Draganito/kicad-mcp/crates/kicad-mcp/src/pads.rs

//! Pad truth and footprint moves, straight from the board.
//!
//! `board_pads` decodes the raw `FootprintInstance` protos KiCad returns
//! over IPC — the **baked** pad positions, not template math. This is the
//! verification tool: a mirrored or mis-rotated part shows up here as pads
//! on the wrong side of the anchor, no 3D render needed.
//!
//! `move_footprint` applies a rigid transform (translate + rotate about the
//! anchor) to the instance and every nested pad, then `UpdateItems` the
//! whole footprint — the same splice path as `connect_pins`, so nets,
//! padstack geometry and the reference survive. No remove+place.

use std::collections::HashMap;

use prost::Message;
use prost_types::Any;

use crate::kicad::Kicad;
use crate::proto_wire::{map_len_fields, set_len_field};

const NM_PER_MM: f64 = 1_000_000.0;
const TYPE_PAD: &str = "type.googleapis.com/kiapi.board.types.Pad";

// Layer / enum codes as in place.rs (kiapi.board.types).
const BL_F_CU: i32 = 3;
const BL_B_CU: i32 = 34;
const PT_PTH: i32 = 1;
const PT_SMD: i32 = 2;
const PT_NPTH: i32 = 4;
const PSS_CIRCLE: i32 = 1;
const PSS_RECTANGLE: i32 = 2;
const PSS_OVAL: i32 = 3;

fn nm_to_mm(nm: i64) -> f64 {
    nm as f64 / NM_PER_MM
}

fn mm_to_nm(mm: f64) -> i64 {
    (mm * NM_PER_MM).round() as i64
}

fn round4(v: f64) -> f64 {
    (v * 10_000.0).round() / 10_000.0
}

#[derive(Debug, Clone, serde::Serialize)]
pub struct PadRow {
    pub reference: String,
    pub pin: String,
    pub net: String,
    pub x_mm: f64,
    pub y_mm: f64,
    pub width_mm: f64,
    pub height_mm: f64,
    pub rotation_deg: f64,
    /// `smd`, `pth`, or `npth`.
    pub kind: String,
    /// `rect`, `oval`, `circle`.
    pub shape: String,
    pub layer: String,
    /// Every copper layer this pad exists on (`F.Cu`, `In1.Cu`, …).
    /// Through-hole wire pads should list the inners — a 5V PTH without
    /// `In1.Cu` cannot take thermals from the power pour.
    pub layers: Vec<String>,
    #[serde(skip_serializing_if = "Option::is_none")]
    pub drill_mm: Option<f64>,
    /// Slot length for oblong drills; absent for round holes.
    #[serde(skip_serializing_if = "Option::is_none")]
    pub drill_h_mm: Option<f64>,
}

/// Baked pad rows for every footprint on the board (IPC raw protos, the
/// positions KiCad actually draws). Optional reference / net filters.
pub async fn board_pads(
    k: &Kicad,
    reference: Option<&str>,
    net: Option<&str>,
) -> Result<Vec<PadRow>, String> {
    let fps = k.footprints().await?;
    let mut ref_of: HashMap<String, String> = HashMap::new();
    for fp in &fps {
        if let (Some(id), Some(r)) = (fp.id.as_deref(), fp.reference.as_deref()) {
            ref_of.insert(id.to_string(), r.to_string());
        }
    }
    let mut net_of: HashMap<String, String> = HashMap::new();
    for entry in k.pad_netlist().await.unwrap_or_default() {
        if let Some(id) = entry.pad_id {
            net_of.insert(id, entry.net_name.unwrap_or_default());
        }
    }
    let copper_count = k
        .summary()
        .await
        .ok()
        .and_then(|s| s.copper_layer_count)
        .unwrap_or(2);
    let raws = k
        .raw_items(vec![kicad_ipc_rs::PcbObjectTypeCode::new_footprint().code])
        .await?;
    let mut rows = Vec::new();
    for raw in &raws {
        let inst = FpInstDec::decode(raw.value.as_slice())
            .map_err(|e| format!("footprint proto decode: {e}"))?;
        let fp_ref = inst
            .id
            .as_ref()
            .and_then(|id| ref_of.get(&id.value))
            .cloned()
            .unwrap_or_default();
        if let Some(want) = reference {
            if fp_ref != want {
                continue;
            }
        }
        let Some(def) = inst.definition else {
            continue;
        };
        for item in &def.items {
            let Some(pad) = decode_pad(item) else {
                continue;
            };
            let pad_net = pad
                .id
                .as_ref()
                .and_then(|id| net_of.get(&id.value))
                .cloned()
                .unwrap_or_default();
            if let Some(want) = net {
                if pad_net != want {
                    continue;
                }
            }
            let pos = pad.position.unwrap_or_default();
            let stack = pad.pad_stack.unwrap_or_default();
            let copper = stack.copper_layers.first();
            let size = copper.and_then(|c| c.size.clone()).unwrap_or_default();
            let copper_ids: Vec<i32> = stack.copper_layers.iter().map(|c| c.layer).collect();
            let layer_ids = crate::copper::copper_layer_ids_from_stack(
                &stack.layers,
                &copper_ids,
                copper_count,
            );
            let layers: Vec<String> = layer_ids
                .iter()
                .copied()
                .map(crate::copper::layer_name)
                .collect();
            rows.push(PadRow {
                reference: fp_ref.clone(),
                pin: pad.number.clone(),
                net: pad_net,
                x_mm: round4(nm_to_mm(pos.x_nm)),
                y_mm: round4(nm_to_mm(pos.y_nm)),
                width_mm: round4(nm_to_mm(size.x_nm)),
                height_mm: round4(nm_to_mm(size.y_nm)),
                rotation_deg: stack.angle.map(|a| a.value_degrees).unwrap_or(0.0),
                kind: match pad.r#type {
                    PT_PTH => "pth",
                    PT_NPTH => "npth",
                    PT_SMD => "smd",
                    _ => "?",
                }
                .into(),
                shape: match copper.map(|c| c.shape) {
                    Some(PSS_CIRCLE) => "circle",
                    Some(PSS_OVAL) => "oval",
                    Some(PSS_RECTANGLE) => "rect",
                    _ => "?",
                }
                .into(),
                layer: layers
                    .first()
                    .cloned()
                    .unwrap_or_else(|| match copper.map(|c| c.layer) {
                        Some(BL_B_CU) => "B.Cu".into(),
                        Some(BL_F_CU) => "F.Cu".into(),
                        Some(other) => format!("L{other}"),
                        None => "?".into(),
                    }),
                layers,
                drill_mm: stack
                    .drill
                    .as_ref()
                    .and_then(|d| d.diameter.as_ref())
                    .map(|v| round4(nm_to_mm(v.x_nm)))
                    .filter(|d| *d > 0.0),
                drill_h_mm: stack
                    .drill
                    .as_ref()
                    .and_then(|d| d.diameter.as_ref())
                    .filter(|v| v.x_nm > 0 && v.y_nm != v.x_nm)
                    .map(|v| round4(nm_to_mm(v.y_nm))),
            });
        }
    }
    rows.sort_by(|a, b| {
        (natural_ref(&a.reference), a.pin.parse::<u32>().ok(), &a.pin).cmp(&(
            natural_ref(&b.reference),
            b.pin.parse::<u32>().ok(),
            &b.pin,
        ))
    });
    Ok(rows)
}

/// `U14` → (`U`, 14) so U2 sorts before U14.
fn natural_ref(r: &str) -> (String, u32) {
    let prefix: String = r.chars().take_while(|c| c.is_ascii_alphabetic()).collect();
    let num = r[prefix.len()..].parse::<u32>().unwrap_or(0);
    (prefix, num)
}

/// Rigid transform in KiCad's y-down frame with visually-CCW positive
/// angles — the same rotation sense as `place::world_xy`. A point at
/// `(px, py)` rides along when the anchor moves from `old` to `new` and
/// the part turns by `delta_deg`.
pub(crate) fn rigid_xy(
    px: f64,
    py: f64,
    old_anchor: (f64, f64),
    new_anchor: (f64, f64),
    delta_deg: f64,
) -> (f64, f64) {
    let rad = delta_deg.to_radians();
    let (s, c) = (rad.sin(), rad.cos());
    let dx = px - old_anchor.0;
    let dy = py - old_anchor.1;
    (
        new_anchor.0 + c * dx + s * dy,
        new_anchor.1 - s * dx + c * dy,
    )
}

/// Patch a raw `FootprintInstance` Any: anchor, orientation, every nested
/// pad (position + padstack angle) and the reference/value text positions.
/// Pure splice — everything not touched (nets, padstack geometry, KIIDs)
/// passes through byte-identical. Returns the patched Any and how many
/// pads were transformed.
pub fn transform_footprint_any(
    fp: &Any,
    old: (f64, f64, f64),
    new: (f64, f64, f64),
) -> Result<(Any, usize), String> {
    let old_anchor = (old.0, old.1);
    let new_anchor = (new.0, new.1);
    let delta_deg = new.2 - old.2;
    let pads_moved = std::cell::Cell::new(0usize);

    // Instance anchor + orientation.
    let mut value = set_len_field(&fp.value, 2, &encode_vec2(new.0, new.1))?;
    value = set_len_field(&value, 3, &encode_angle(new.2))?;

    // Reference/value text on the instance (fields 7/8).
    for field in [7u32, 8u32] {
        value = map_len_fields(&value, field, |f| {
            patch_field_text_pos(f, old_anchor, new_anchor, delta_deg)
        })?;
    }

    // Definition: nested pads + its own reference/value fields.
    value = map_len_fields(&value, 6, |def| {
        let mut def = map_len_fields(def, 11, |item_bytes| {
            let item = match Any::decode(item_bytes) {
                Ok(item) => item,
                Err(_) => return Ok(item_bytes.to_vec()),
            };
            let Some(pad) = decode_pad(&item) else {
                return Ok(item_bytes.to_vec());
            };
            let pos = pad.position.unwrap_or_default();
            let (nx, ny) = rigid_xy(
                nm_to_mm(pos.x_nm),
                nm_to_mm(pos.y_nm),
                old_anchor,
                new_anchor,
                delta_deg,
            );
            let mut pad_value = set_len_field(&item.value, 7, &encode_vec2(nx, ny))?;
            if delta_deg.abs() > 1e-9 {
                let new_angle = pad
                    .pad_stack
                    .as_ref()
                    .and_then(|s| s.angle.as_ref())
                    .map(|a| a.value_degrees)
                    .unwrap_or(0.0)
                    + delta_deg;
                pad_value = map_len_fields(&pad_value, 6, |stack| {
                    set_len_field(stack, 6, &encode_angle(new_angle))
                })?;
            }
            pads_moved.set(pads_moved.get() + 1);
            let patched = Any {
                type_url: if item.type_url.is_empty() {
                    TYPE_PAD.into()
                } else {
                    item.type_url
                },
                value: pad_value,
            };
            Ok(patched.encode_to_vec())
        })?;
        for field in [7u32, 8u32] {
            def = map_len_fields(&def, field, |f| {
                patch_field_text_pos(f, old_anchor, new_anchor, delta_deg)
            })?;
        }
        Ok(def)
    })?;

    if pads_moved.get() == 0 {
        return Err(
            "footprint proto has no pads — refusing a move that would strand copper".into(),
        );
    }
    Ok((
        Any {
            type_url: fp.type_url.clone(),
            value,
        },
        pads_moved.get(),
    ))
}

/// Field (tag 3 BoardText → tag 2 Text → tag 2 position): ride the text
/// along with the part so the silk refdes does not stay behind.
fn patch_field_text_pos(
    field_bytes: &[u8],
    old_anchor: (f64, f64),
    new_anchor: (f64, f64),
    delta_deg: f64,
) -> Result<Vec<u8>, String> {
    map_len_fields(field_bytes, 3, |board_text| {
        map_len_fields(board_text, 2, |text| {
            let decoded = TextDec::decode(text).unwrap_or_default();
            let Some(pos) = decoded.position else {
                return Ok(text.to_vec());
            };
            let (nx, ny) = rigid_xy(
                nm_to_mm(pos.x_nm),
                nm_to_mm(pos.y_nm),
                old_anchor,
                new_anchor,
                delta_deg,
            );
            set_len_field(text, 2, &encode_vec2(nx, ny))
        })
    })
}

/// Move / rotate one placed footprint. Courtyard-checked at the target,
/// nets untouched, one undo. Copper does not move.
pub async fn move_footprint(
    k: &Kicad,
    reference: &str,
    x_mm: f64,
    y_mm: f64,
    rotation_deg: Option<f64>,
) -> Result<serde_json::Value, String> {
    let fps = k.footprints().await?;
    let me = fps
        .iter()
        .find(|f| f.reference.as_deref() == Some(reference))
        .ok_or_else(|| format!("{reference} is not on the board"))?;
    let id = me
        .id
        .clone()
        .ok_or_else(|| format!("{reference} has no KIID over IPC"))?;
    let old = (
        me.x_mm.unwrap_or(0.0),
        me.y_mm.unwrap_or(0.0),
        me.rotation_deg.unwrap_or(0.0),
    );
    let new_rot = rotation_deg.unwrap_or(old.2);

    // Courtyard check at the target, against everything except this part.
    let dir = k.project_dir().await?;
    let pretty = crate::kicad::jlc_pretty_dir(&dir);
    let mut note = String::new();
    match me
        .value
        .as_deref()
        .and_then(|t| crate::place::courtyard_of_template(&pretty, t))
    {
        Some(local) => {
            let new_box = crate::place::aabb_at(&local, x_mm, y_mm, new_rot);
            for other in &fps {
                if other.reference.as_deref() == Some(reference) {
                    continue;
                }
                let Some(tmpl) = other.value.as_deref() else {
                    continue;
                };
                let Some(other_local) = crate::place::courtyard_of_template(&pretty, tmpl) else {
                    continue;
                };
                let other_box = crate::place::aabb_at(
                    &other_local,
                    other.x_mm.unwrap_or(0.0),
                    other.y_mm.unwrap_or(0.0),
                    other.rotation_deg.unwrap_or(0.0),
                );
                if new_box.overlaps(&other_box, 0.0) {
                    return Err(format!(
                        "courtyard of {reference} at ({x_mm:.2}, {y_mm:.2}) overlaps {} — pick free space (F.CrtYd)",
                        other.reference.as_deref().unwrap_or(tmpl)
                    ));
                }
            }
        }
        None => {
            note.push_str("no courtyard template found — overlap not checked. ");
        }
    }

    let raws = k
        .raw_items(vec![kicad_ipc_rs::PcbObjectTypeCode::new_footprint().code])
        .await?;
    let raw = raws
        .iter()
        .find(|r| {
            FpHead::decode(r.value.as_slice())
                .ok()
                .and_then(|h| h.id)
                .map(|k| k.value == id)
                .unwrap_or(false)
        })
        .ok_or_else(|| format!("{reference}: raw footprint proto not found over IPC"))?;

    let (patched, pads_moved) = transform_footprint_any(raw, old, (x_mm, y_mm, new_rot))?;

    let session = k.begin_commit().await?;
    match k.update_items(vec![patched]).await {
        Ok(_) => {
            k.end_commit(session, &format!("kicad-mcp move {reference}"))
                .await?;
            let _ = k.refresh().await;
            note.push_str("Copper does not move — re-route tracks that reached this part.");
            Ok(serde_json::json!({
                "ok": true,
                "reference": reference,
                "from": { "x_mm": old.0, "y_mm": old.1, "rotation_deg": old.2 },
                "to": { "x_mm": x_mm, "y_mm": y_mm, "rotation_deg": new_rot },
                "pads_moved": pads_moved,
                "note": note,
            }))
        }
        Err(e) => {
            let _ = k.drop_commit(session).await;
            Err(e)
        }
    }
}

/// One pad reduced to comparable geometry — either recomputed from the
/// template (expected) or decoded from the board (actual).
#[derive(Debug, Clone)]
pub(crate) struct GeomPad {
    pub number: String,
    pub x_mm: f64,
    pub y_mm: f64,
    pub width_mm: f64,
    pub height_mm: f64,
    pub angle_deg: f64,
    /// `smd`, `pth`, `npth`.
    pub kind: &'static str,
    /// Circles have no meaningful angle.
    pub circle: bool,
    /// Drill diameter (x, y). Round hole: x == y. None: no hole.
    pub drill_mm: Option<(f64, f64)>,
}

fn geom_from_template(p: &crate::place::ModPad, spec: &crate::place::PlaceSpec<'_>) -> GeomPad {
    use crate::place::{ModPadKind, ModPadShape};
    let (x, y) = crate::place::world_xy(p.x_mm, p.y_mm, spec);
    GeomPad {
        number: p.number.clone(),
        x_mm: x,
        y_mm: y,
        width_mm: p.width_mm,
        height_mm: p.height_mm,
        angle_deg: p.rot_deg + spec.rotation_deg,
        kind: match p.kind {
            ModPadKind::Npth => "npth",
            ModPadKind::ThruHole => "pth",
            ModPadKind::SmdFront | ModPadKind::SmdBack => "smd",
        },
        circle: p.shape == ModPadShape::Circle,
        drill_mm: p.drill_mm.map(|d| (d, p.drill_h_mm.unwrap_or(d))),
    }
}

fn geom_from_board(p: &PadDec) -> Option<GeomPad> {
    let pos = p.position.clone()?;
    let stack = p.pad_stack.clone().unwrap_or_default();
    let copper = stack.copper_layers.first();
    let size = copper.and_then(|c| c.size.clone()).unwrap_or_default();
    Some(GeomPad {
        number: p.number.clone(),
        x_mm: nm_to_mm(pos.x_nm),
        y_mm: nm_to_mm(pos.y_nm),
        width_mm: nm_to_mm(size.x_nm),
        height_mm: nm_to_mm(size.y_nm),
        angle_deg: stack.angle.as_ref().map(|a| a.value_degrees).unwrap_or(0.0),
        kind: match p.r#type {
            PT_PTH => "pth",
            PT_NPTH => "npth",
            PT_SMD => "smd",
            _ => "?",
        },
        circle: copper.map(|c| c.shape) == Some(PSS_CIRCLE),
        drill_mm: stack
            .drill
            .as_ref()
            .and_then(|d| d.diameter.as_ref())
            .filter(|v| v.x_nm > 0)
            .map(|v| (nm_to_mm(v.x_nm), nm_to_mm(v.y_nm))),
    })
}

/// Shortest signed distance between two angles, in degrees.
fn angle_diff_deg(a: f64, b: f64) -> f64 {
    let mut d = (a - b) % 360.0;
    if d > 180.0 {
        d -= 360.0;
    }
    if d < -180.0 {
        d += 360.0;
    }
    d.abs()
}

const ANGLE_TOL_DEG: f64 = 0.5;
const PROBLEM_CAP: usize = 10;

/// Compare expected (template @ anchor+rotation) against actual (baked
/// board pads). Pads are grouped by pin number and matched nearest-first,
/// so thermal clusters with one shared number work. Returns one problem
/// row per mismatch — empty means the footprint is placed exactly as its
/// template says. A mirrored part fails with y-deltas, a wrong rotation
/// sense fails with swapped axes, a stale bake fails on every pad.
pub(crate) fn diff_pads(
    expected: &[GeomPad],
    actual: &[GeomPad],
    tol_mm: f64,
) -> Vec<serde_json::Value> {
    let mut problems = Vec::new();
    let mut numbers: Vec<&str> = expected
        .iter()
        .chain(actual.iter())
        .map(|p| p.number.as_str())
        .collect();
    numbers.sort_unstable();
    numbers.dedup();
    for num in numbers {
        let exp: Vec<&GeomPad> = expected.iter().filter(|p| p.number == num).collect();
        let mut act: Vec<&GeomPad> = actual.iter().filter(|p| p.number == num).collect();
        if exp.len() != act.len() {
            problems.push(serde_json::json!({
                "pin": num,
                "problem": "pad_count",
                "expected": exp.len(),
                "actual": act.len(),
            }));
            continue;
        }
        for e in exp {
            let (idx, _) = act
                .iter()
                .enumerate()
                .min_by(|(_, a), (_, b)| {
                    let da = (a.x_mm - e.x_mm).hypot(a.y_mm - e.y_mm);
                    let db = (b.x_mm - e.x_mm).hypot(b.y_mm - e.y_mm);
                    da.partial_cmp(&db).unwrap_or(std::cmp::Ordering::Equal)
                })
                .expect("same length as exp");
            let a = act.remove(idx);
            let delta = (a.x_mm - e.x_mm).hypot(a.y_mm - e.y_mm);
            if delta > tol_mm {
                problems.push(serde_json::json!({
                    "pin": num,
                    "problem": "position",
                    "expected_x_mm": round4(e.x_mm),
                    "expected_y_mm": round4(e.y_mm),
                    "actual_x_mm": round4(a.x_mm),
                    "actual_y_mm": round4(a.y_mm),
                    "delta_mm": round4(delta),
                }));
                continue;
            }
            if e.kind != a.kind {
                problems.push(serde_json::json!({
                    "pin": num,
                    "problem": "pad_type",
                    "expected": e.kind,
                    "actual": a.kind,
                }));
            }
            if (e.width_mm - a.width_mm).abs() > tol_mm
                || (e.height_mm - a.height_mm).abs() > tol_mm
            {
                problems.push(serde_json::json!({
                    "pin": num,
                    "problem": "size",
                    "expected_mm": [round4(e.width_mm), round4(e.height_mm)],
                    "actual_mm": [round4(a.width_mm), round4(a.height_mm)],
                }));
            }
            if !e.circle && angle_diff_deg(e.angle_deg, a.angle_deg) > ANGLE_TOL_DEG {
                problems.push(serde_json::json!({
                    "pin": num,
                    "problem": "angle",
                    "expected_deg": e.angle_deg,
                    "actual_deg": a.angle_deg,
                }));
            }
            // Missing hole, extra hole, wrong diameter, or a slot baked as a
            // round hole (drill y collapsed to x) all fail here.
            let drill_ok = match (e.drill_mm, a.drill_mm) {
                (None, None) => true,
                (Some((ex, ey)), Some((ax, ay))) => {
                    (ex - ax).abs() <= tol_mm && (ey - ay).abs() <= tol_mm
                }
                _ => false,
            };
            if !drill_ok {
                problems.push(serde_json::json!({
                    "pin": num,
                    "problem": "drill",
                    "expected_mm": e.drill_mm.map(|(x, y)| [round4(x), round4(y)]),
                    "actual_mm": a.drill_mm.map(|(x, y)| [round4(x), round4(y)]),
                }));
            }
        }
    }
    problems
}

/// Hard OK/fail placement audit: recompute every pad from the template at
/// the footprint's anchor + rotation, compare against the baked board pads.
pub async fn check_placement(
    k: &Kicad,
    reference: Option<&str>,
    tolerance_mm: f64,
) -> Result<serde_json::Value, String> {
    if !(0.0001..=1.0).contains(&tolerance_mm) {
        return Err("tolerance_mm must be between 0.0001 and 1.0".into());
    }
    let dir = k.project_dir().await?;
    let pretty = crate::kicad::jlc_pretty_dir(&dir);
    let fps = k.footprints().await?;
    let raws = k
        .raw_items(vec![kicad_ipc_rs::PcbObjectTypeCode::new_footprint().code])
        .await?;
    let mut actual_by_id: HashMap<String, Vec<GeomPad>> = HashMap::new();
    for raw in &raws {
        let Ok(inst) = FpInstDec::decode(raw.value.as_slice()) else {
            continue;
        };
        let Some(id) = inst.id else { continue };
        let pads = inst
            .definition
            .map(|def| {
                def.items
                    .iter()
                    .filter_map(decode_pad)
                    .filter_map(|p| geom_from_board(&p))
                    .collect()
            })
            .unwrap_or_default();
        actual_by_id.insert(id.value, pads);
    }

    let mut templates: HashMap<String, Result<Vec<crate::place::ModPad>, String>> = HashMap::new();
    let mut passed: Vec<String> = Vec::new();
    let mut failed: Vec<serde_json::Value> = Vec::new();
    let mut skipped: Vec<serde_json::Value> = Vec::new();
    let mut matched_filter = false;

    for fp in &fps {
        let Some(r) = fp.reference.as_deref() else {
            continue;
        };
        if let Some(want) = reference {
            if r != want {
                continue;
            }
        }
        matched_filter = true;
        let skip = |reason: &str| serde_json::json!({ "reference": r, "reason": reason });
        let Some(template) = fp.value.as_deref() else {
            skipped.push(skip("footprint has no template name (value field)"));
            continue;
        };
        let entry = templates
            .entry(template.to_string())
            .or_insert_with(|| crate::place::load_template(&pretty, template).map(|t| t.pads));
        let tpl_pads = match entry {
            Ok(p) => p.clone(),
            Err(e) => {
                skipped.push(skip(&format!("template not verifiable: {e}")));
                continue;
            }
        };
        let Some(actual) = fp.id.as_deref().and_then(|id| actual_by_id.get(id)) else {
            skipped.push(skip("raw footprint proto not found over IPC"));
            continue;
        };
        let spec = crate::place::PlaceSpec {
            template,
            reference: r,
            x_mm: fp.x_mm.unwrap_or(0.0),
            y_mm: fp.y_mm.unwrap_or(0.0),
            rotation_deg: fp.rotation_deg.unwrap_or(0.0),
            pads: &[],
        };
        let expected: Vec<GeomPad> = tpl_pads
            .iter()
            .map(|p| geom_from_template(p, &spec))
            .collect();
        let mut problems = diff_pads(&expected, actual, tolerance_mm);
        if problems.is_empty() {
            passed.push(r.to_string());
        } else {
            let truncated = problems.len() > PROBLEM_CAP;
            let total = problems.len();
            problems.truncate(PROBLEM_CAP);
            failed.push(serde_json::json!({
                "reference": r,
                "template": template,
                "x_mm": spec.x_mm,
                "y_mm": spec.y_mm,
                "rotation_deg": spec.rotation_deg,
                "problem_count": total,
                "problems": problems,
                "problems_truncated": truncated,
            }));
        }
    }

    if reference.is_some() && !matched_filter {
        return Err(format!(
            "{} is not on the board",
            reference.unwrap_or_default()
        ));
    }
    passed.sort_by_key(|r| natural_ref(r));
    Ok(serde_json::json!({
        "ok": failed.is_empty(),
        "checked": passed.len() + failed.len(),
        "failed_count": failed.len(),
        "failed": failed,
        "passed": passed,
        "skipped": skipped,
        "tolerance_mm": tolerance_mm,
    }))
}

fn decode_pad(item: &Any) -> Option<PadDec> {
    if !item.type_url.is_empty() && !item.type_url.contains("Pad") {
        return None;
    }
    PadDec::decode(item.value.as_slice()).ok()
}

fn encode_vec2(x_mm: f64, y_mm: f64) -> Vec<u8> {
    Vec2Dec {
        x_nm: mm_to_nm(x_mm),
        y_nm: mm_to_nm(y_mm),
    }
    .encode_to_vec()
}

fn encode_angle(deg: f64) -> Vec<u8> {
    AngleDec { value_degrees: deg }.encode_to_vec()
}

// --- decode mirrors of the kiapi.board.types wire format (see place.rs) ---

#[derive(Clone, PartialEq, Message)]
struct KiidDec {
    #[prost(string, tag = "1")]
    value: String,
}

#[derive(Clone, PartialEq, Message)]
struct Vec2Dec {
    #[prost(int64, tag = "1")]
    x_nm: i64,
    #[prost(int64, tag = "2")]
    y_nm: i64,
}

#[derive(Clone, PartialEq, Message)]
struct AngleDec {
    #[prost(double, tag = "1")]
    value_degrees: f64,
}

#[derive(Clone, PartialEq, Message)]
struct DrillDec {
    #[prost(message, optional, tag = "3")]
    diameter: Option<Vec2Dec>,
}

#[derive(Clone, PartialEq, Message)]
struct PadStackLayerDec {
    #[prost(int32, tag = "1")]
    layer: i32,
    #[prost(int32, tag = "2")]
    shape: i32,
    #[prost(message, optional, tag = "3")]
    size: Option<Vec2Dec>,
}

#[derive(Clone, PartialEq, Message)]
struct PadStackDec {
    #[prost(int32, tag = "1")]
    r#type: i32,
    #[prost(int32, repeated, tag = "2")]
    layers: Vec<i32>,
    #[prost(message, optional, tag = "3")]
    drill: Option<DrillDec>,
    #[prost(message, repeated, tag = "5")]
    copper_layers: Vec<PadStackLayerDec>,
    #[prost(message, optional, tag = "6")]
    angle: Option<AngleDec>,
}

/// `net` (field 4) is deliberately not decoded — a shape mismatch there
/// would fail the whole pad (see nets.rs `PadHead`). Nets come from the
/// official pad netlist, joined by KIID.
#[derive(Clone, PartialEq, Message)]
struct PadDec {
    #[prost(message, optional, tag = "1")]
    id: Option<KiidDec>,
    #[prost(string, tag = "3")]
    number: String,
    #[prost(int32, tag = "5")]
    r#type: i32,
    #[prost(message, optional, tag = "6")]
    pad_stack: Option<PadStackDec>,
    #[prost(message, optional, tag = "7")]
    position: Option<Vec2Dec>,
}

#[derive(Clone, PartialEq, Message)]
struct FpDefDec {
    #[prost(message, repeated, tag = "11")]
    items: Vec<Any>,
}

#[derive(Clone, PartialEq, Message)]
struct FpInstDec {
    #[prost(message, optional, tag = "1")]
    id: Option<KiidDec>,
    #[prost(message, optional, tag = "2")]
    position: Option<Vec2Dec>,
    #[prost(message, optional, tag = "3")]
    orientation: Option<AngleDec>,
    #[prost(message, optional, tag = "6")]
    definition: Option<FpDefDec>,
}

#[derive(Clone, PartialEq, Message)]
struct FpHead {
    #[prost(message, optional, tag = "1")]
    id: Option<KiidDec>,
}

#[derive(Clone, PartialEq, Message)]
struct TextDec {
    #[prost(message, optional, tag = "2")]
    position: Option<Vec2Dec>,
}

#[cfg(test)]
mod tests {
    use super::*;
    use crate::place::{footprint_instance_any, ModPad, ModPadKind, ModPadShape, PlaceSpec};

    fn two_pads() -> Vec<ModPad> {
        let pad = |n: &str, px: f64| ModPad {
            number: n.into(),
            kind: ModPadKind::SmdFront,
            shape: ModPadShape::Rect,
            x_mm: px,
            y_mm: 0.0,
            rot_deg: 0.0,
            width_mm: 0.8,
            height_mm: 0.9,
            drill_mm: None,
            drill_h_mm: None,
            mask: true,
        };
        vec![pad("1", -0.75), pad("2", 0.75)]
    }

    fn instance(x: f64, y: f64, rot: f64, pads: &[ModPad]) -> Any {
        footprint_instance_any(&PlaceSpec {
            template: "T",
            reference: "R1",
            x_mm: x,
            y_mm: y,
            rotation_deg: rot,
            pads,
        })
        .unwrap()
    }

    fn decoded_pads(any: &Any) -> Vec<(String, f64, f64)> {
        let inst = FpInstDec::decode(any.value.as_slice()).unwrap();
        inst.definition
            .unwrap()
            .items
            .iter()
            .filter_map(decode_pad)
            .map(|p| {
                let pos = p.position.unwrap();
                (p.number, nm_to_mm(pos.x_nm), nm_to_mm(pos.y_nm))
            })
            .collect()
    }

    #[test]
    fn decodes_baked_pad_positions() {
        let pads = two_pads();
        let any = instance(100.0, 80.0, 0.0, &pads);
        let rows = decoded_pads(&any);
        assert_eq!(rows.len(), 2);
        let p1 = rows.iter().find(|r| r.0 == "1").unwrap();
        assert!((p1.1 - 99.25).abs() < 1e-6);
        assert!((p1.2 - 80.0).abs() < 1e-6);
    }

    #[test]
    fn rigid_translation_keeps_offsets() {
        let (x, y) = rigid_xy(101.0, 80.5, (100.0, 80.0), (140.0, 60.0), 0.0);
        assert!((x - 141.0).abs() < 1e-9);
        assert!((y - 60.5).abs() < 1e-9);
    }

    /// Same rotation-sense guard as place::world_xy: +90° is visually CCW,
    /// so a pad east of the anchor must land north (smaller y, y-down frame).
    #[test]
    fn rigid_plus_90_is_counterclockwise_on_screen() {
        let (x, y) = rigid_xy(103.0, 80.0, (100.0, 80.0), (100.0, 80.0), 90.0);
        assert!((x - 100.0).abs() < 1e-9);
        assert!(
            (y - 77.0).abs() < 1e-9,
            "east pad must land north, got y={y}"
        );
    }

    #[test]
    fn transform_moves_anchor_and_pads_together() {
        let pads = two_pads();
        let any = instance(100.0, 80.0, 0.0, &pads);
        let (patched, moved) =
            transform_footprint_any(&any, (100.0, 80.0, 0.0), (150.0, 90.0, 0.0)).unwrap();
        assert_eq!(moved, 2);
        let inst = FpInstDec::decode(patched.value.as_slice()).unwrap();
        let anchor = inst.position.unwrap();
        assert!((nm_to_mm(anchor.x_nm) - 150.0).abs() < 1e-6);
        assert!((nm_to_mm(anchor.y_nm) - 90.0).abs() < 1e-6);
        let rows = decoded_pads(&patched);
        let p2 = rows.iter().find(|r| r.0 == "2").unwrap();
        assert!((p2.1 - 150.75).abs() < 1e-6);
        assert!((p2.2 - 90.0).abs() < 1e-6);
    }

    #[test]
    fn transform_rotates_pads_ccw_and_sets_orientation() {
        let pads = two_pads();
        let any = instance(100.0, 80.0, 0.0, &pads);
        let (patched, _) =
            transform_footprint_any(&any, (100.0, 80.0, 0.0), (100.0, 80.0, 90.0)).unwrap();
        let inst = FpInstDec::decode(patched.value.as_slice()).unwrap();
        assert!((inst.orientation.unwrap().value_degrees - 90.0).abs() < 1e-9);
        let rows = decoded_pads(&patched);
        // Pad 2 sat east of the anchor; after +90° (visually CCW) it is north.
        let p2 = rows.iter().find(|r| r.0 == "2").unwrap();
        assert!((p2.1 - 100.0).abs() < 1e-6);
        assert!(
            (p2.2 - 79.25).abs() < 1e-6,
            "expected north of anchor, got y={}",
            p2.2
        );
        // Pad angle followed the delta.
        let def = FpInstDec::decode(patched.value.as_slice())
            .unwrap()
            .definition
            .unwrap();
        let angles: Vec<f64> = def
            .items
            .iter()
            .filter_map(decode_pad)
            .filter_map(|p| p.pad_stack.and_then(|s| s.angle).map(|a| a.value_degrees))
            .collect();
        assert!(angles.iter().all(|a| (a - 90.0).abs() < 1e-9));
    }

    #[test]
    fn transform_matches_fresh_placement() {
        // Moving 0°→90° must land pads exactly where placing at 90° would.
        let pads = two_pads();
        let placed_at_0 = instance(100.0, 80.0, 0.0, &pads);
        let placed_at_90 = instance(120.0, 70.0, 90.0, &pads);
        let (moved, _) =
            transform_footprint_any(&placed_at_0, (100.0, 80.0, 0.0), (120.0, 70.0, 90.0)).unwrap();
        let a = decoded_pads(&moved);
        let b = decoded_pads(&placed_at_90);
        for (pa, pb) in a.iter().zip(b.iter()) {
            assert_eq!(pa.0, pb.0);
            assert!(
                (pa.1 - pb.1).abs() < 1e-6,
                "{} x {} vs {}",
                pa.0,
                pa.1,
                pb.1
            );
            assert!(
                (pa.2 - pb.2).abs() < 1e-6,
                "{} y {} vs {}",
                pa.0,
                pa.2,
                pb.2
            );
        }
    }

    fn geoms_from_instance(any: &Any) -> Vec<GeomPad> {
        FpInstDec::decode(any.value.as_slice())
            .unwrap()
            .definition
            .unwrap()
            .items
            .iter()
            .filter_map(decode_pad)
            .filter_map(|p| geom_from_board(&p))
            .collect()
    }

    fn expected_geoms(pads: &[ModPad], x: f64, y: f64, rot: f64) -> Vec<GeomPad> {
        let spec = PlaceSpec {
            template: "T",
            reference: "R1",
            x_mm: x,
            y_mm: y,
            rotation_deg: rot,
            pads: &[],
        };
        pads.iter().map(|p| geom_from_template(p, &spec)).collect()
    }

    /// A part baked by the fixed pipeline must pass at every rotation —
    /// template math and pad bake are the same formula.
    #[test]
    fn placement_check_passes_for_correct_bake() {
        let pads = two_pads();
        for rot in [0.0, 90.0, 180.0, -90.0] {
            let inst = instance(100.0, 80.0, rot, &pads);
            let actual = geoms_from_instance(&inst);
            let expected = expected_geoms(&pads, 100.0, 80.0, rot);
            let problems = diff_pads(&expected, &actual, 0.01);
            assert!(problems.is_empty(), "rot {rot}: {problems:?}");
        }
    }

    /// The old converter bug: every pad vertically mirrored about the anchor.
    #[test]
    fn placement_check_fails_for_mirrored_pads() {
        let pad = |n: &str, y: f64| ModPad {
            number: n.into(),
            kind: ModPadKind::SmdFront,
            shape: ModPadShape::Rect,
            x_mm: 0.0,
            y_mm: y,
            rot_deg: 0.0,
            width_mm: 0.8,
            height_mm: 0.9,
            drill_mm: None,
            drill_h_mm: None,
            mask: true,
        };
        let asym = vec![pad("1", -1.5), pad("2", 0.5)];
        let expected = expected_geoms(&asym, 100.0, 80.0, 0.0);
        let mut actual = expected.clone();
        for a in &mut actual {
            a.y_mm = 80.0 - (a.y_mm - 80.0); // mirror about the anchor
        }
        let problems = diff_pads(&expected, &actual, 0.01);
        assert_eq!(problems.len(), 2, "{problems:?}");
        assert!(problems.iter().all(|p| p["problem"] == "position"));
        // Pin 1 sat 1.5 mm north; mirrored it is 1.5 mm south → 3 mm off.
        let p1 = problems.iter().find(|p| p["pin"] == "1").unwrap();
        assert!((p1["delta_mm"].as_f64().unwrap() - 3.0).abs() < 1e-6);
    }

    /// The old rotation-sense bug: pads baked clockwise while the
    /// orientation field claims counterclockwise.
    #[test]
    fn placement_check_fails_for_clockwise_bake() {
        let pads = two_pads();
        let expected = expected_geoms(&pads, 100.0, 80.0, 90.0);
        // Clockwise bake: east pad lands south instead of north.
        let mut actual = expected.clone();
        for a in &mut actual {
            a.y_mm = 80.0 - (a.y_mm - 80.0);
        }
        let problems = diff_pads(&expected, &actual, 0.01);
        assert_eq!(problems.len(), 2, "{problems:?}");
        let p2 = problems.iter().find(|p| p["pin"] == "2").unwrap();
        assert!((p2["delta_mm"].as_f64().unwrap() - 1.5).abs() < 1e-6);
    }

    /// A stale bake: the orientation field says 180° but the pads still
    /// sit where a 0° placement put them (e.g. rotated in a buggy build).
    #[test]
    fn placement_check_fails_for_stale_bake() {
        let pads = two_pads();
        let inst_at_0 = instance(100.0, 80.0, 0.0, &pads);
        let actual = geoms_from_instance(&inst_at_0);
        let expected = expected_geoms(&pads, 100.0, 80.0, 180.0);
        let problems = diff_pads(&expected, &actual, 0.01);
        assert_eq!(problems.len(), 2, "{problems:?}");
        assert!(problems.iter().all(|p| p["problem"] == "position"));
    }

    #[test]
    fn placement_check_flags_count_size_and_angle() {
        let pads = two_pads();
        let expected = expected_geoms(&pads, 0.0, 0.0, 0.0);
        // Missing pad.
        let problems = diff_pads(&expected, &expected[..1], 0.01);
        assert!(problems.iter().any(|p| p["problem"] == "pad_count"));
        // Wrong size.
        let mut fat = expected.clone();
        fat[0].width_mm += 0.2;
        let problems = diff_pads(&expected, &fat, 0.01);
        assert!(problems.iter().any(|p| p["problem"] == "size"));
        // Wrong pad angle (rect turned 90°).
        let mut turned = expected.clone();
        turned[1].angle_deg = 90.0;
        let problems = diff_pads(&expected, &turned, 0.01);
        assert!(problems.iter().any(|p| p["problem"] == "angle"));
        // Full turns are not a mismatch.
        let mut wrapped = expected.clone();
        wrapped[1].angle_deg = 360.0;
        assert!(diff_pads(&expected, &wrapped, 0.01).is_empty());
    }

    /// The USB-C regression: a template slot (0.6×1.7 oblong drill) baked
    /// as a 0.6 round hole, and an NPTH peg baked as a drill-less SMD pad —
    /// both must fail the audit with a drill / pad_type problem.
    #[test]
    fn placement_check_fails_for_lost_holes() {
        let slot = GeomPad {
            number: "1".into(),
            x_mm: 4.325,
            y_mm: -1.7057,
            width_mm: 0.9,
            height_mm: 2.0,
            angle_deg: 0.0,
            kind: "pth",
            circle: false,
            drill_mm: Some((0.6, 1.7)),
        };
        let peg = GeomPad {
            number: "".into(),
            x_mm: 2.89,
            y_mm: -1.1541,
            width_mm: 0.6,
            height_mm: 0.6,
            angle_deg: 0.0,
            kind: "npth",
            circle: true,
            drill_mm: Some((0.6, 0.6)),
        };
        let expected = vec![slot.clone(), peg.clone()];
        // The stale bake: slot drill collapsed to a circle, peg became SMD
        // without any hole.
        let actual = vec![
            GeomPad {
                drill_mm: Some((0.6, 0.6)),
                ..slot
            },
            GeomPad {
                kind: "smd",
                drill_mm: None,
                ..peg
            },
        ];
        let problems = diff_pads(&expected, &actual, 0.01);
        assert!(
            problems
                .iter()
                .any(|p| p["pin"] == "1" && p["problem"] == "drill"),
            "{problems:?}"
        );
        assert!(problems
            .iter()
            .any(|p| p["pin"] == "" && p["problem"] == "pad_type"));
        assert!(problems
            .iter()
            .any(|p| p["pin"] == "" && p["problem"] == "drill"));
        // The correct bake passes.
        assert!(diff_pads(&expected, &expected.clone(), 0.01).is_empty());
    }

    /// Thermal clusters: several pads share one number; matching is by
    /// nearest position, so order must not matter.
    #[test]
    fn placement_check_handles_shared_pin_numbers() {
        let pad = |x: f64, y: f64| GeomPad {
            number: "41".into(),
            x_mm: x,
            y_mm: y,
            width_mm: 1.0,
            height_mm: 1.0,
            angle_deg: 0.0,
            kind: "smd",
            circle: false,
            drill_mm: None,
        };
        let expected = vec![pad(10.0, 10.0), pad(12.0, 10.0), pad(11.0, 12.0)];
        let shuffled = vec![pad(11.0, 12.0), pad(10.0, 10.0), pad(12.0, 10.0)];
        assert!(diff_pads(&expected, &shuffled, 0.01).is_empty());
        let mut off = shuffled.clone();
        off[1].x_mm += 0.5;
        let problems = diff_pads(&expected, &off, 0.01);
        assert_eq!(problems.len(), 1);
        assert_eq!(problems[0]["problem"], "position");
    }

    #[test]
    fn transform_preserves_pad_numbers_and_sizes() {
        let pads = two_pads();
        let any = instance(100.0, 80.0, 0.0, &pads);
        let (patched, _) =
            transform_footprint_any(&any, (100.0, 80.0, 0.0), (150.0, 90.0, 90.0)).unwrap();
        let inst = FpInstDec::decode(patched.value.as_slice()).unwrap();
        for item in &inst.definition.unwrap().items {
            let pad = decode_pad(item).unwrap();
            assert!(pad.number == "1" || pad.number == "2");
            let size = pad.pad_stack.unwrap().copper_layers[0]
                .size
                .clone()
                .unwrap();
            assert!((nm_to_mm(size.x_nm) - 0.8).abs() < 1e-6);
            assert!((nm_to_mm(size.y_nm) - 0.9).abs() < 1e-6);
        }
    }
}
