Draganito/kicad-mcp/crates/kicad-mcp/src/nets.rs

//! Join two pads onto one net (`Pad.net` via `UpdateItems` of the parent
//! footprint — KiCad rejects a free pad: "Tried to create a pad in UNDEFINED").
//! `disconnect_pin` is the inverse: splice net code 0 / name `"unconnected"`.
//!
//! Nested pad payloads are spliced in place so padstack geometry survives.
//! KiCad 10 persists `Pad.net` / `Track.net` after UpdateItems. KiCad 9.0.2
//! accepted the call but dropped the net on save — do not use 9 for nets.

use std::collections::HashMap;

use kicad_ipc_rs::model::board::PadNetEntry;
use kicad_ipc_rs::PcbObjectTypeCode;
use prost::Message;
use prost_types::Any;

use crate::kicad::Kicad;
use crate::proto_wire::{encode_net, encode_unconnected, map_len_fields, set_len_field};

const TYPE_PAD: &str = "type.googleapis.com/kiapi.board.types.Pad";
const TYPE_FOOTPRINT: &str = "type.googleapis.com/kiapi.board.types.FootprintInstance";

#[derive(Clone, Debug)]
pub struct PinRef {
    pub reference: String,
    pub pin: String,
}

pub fn named_net(name: Option<&str>) -> Option<String> {
    match name.map(str::trim) {
        None | Some("") | Some("unconnected") => None,
        Some(n) => Some(n.to_string()),
    }
}

pub fn resolve_net_name(
    a: Option<&str>,
    b: Option<&str>,
    hint: Option<&str>,
    fallback: &str,
) -> Result<String, String> {
    let a = named_net(a);
    let b = named_net(b);
    let hint = named_net(hint);
    match (a.as_deref(), b.as_deref(), hint.as_deref()) {
        (Some(x), Some(y), _) if x != y => Err(format!(
            "pads already sit on two different nets ({x} and {y})"
        )),
        (Some(x), _, Some(h)) | (_, Some(x), Some(h)) if x != h => {
            Err(format!("pad is already on {x}, cannot assign {h}"))
        }
        (Some(x), _, _) | (_, Some(x), _) => Ok(x.to_string()),
        (None, None, Some(h)) => Ok(h.to_string()),
        (None, None, None) => Ok(fallback.to_string()),
    }
}

pub async fn connect_pairs(
    k: &Kicad,
    pairs: &[(PinRef, PinRef, Option<String>)],
) -> Result<Vec<serde_json::Value>, String> {
    if pairs.is_empty() {
        return Err("connect_pins needs at least one pair".into());
    }
    if pairs.len() > crate::place::PLACE_MAX {
        return Err(format!(
            "connect_many max {} pairs (got {})",
            crate::place::PLACE_MAX,
            pairs.len()
        ));
    }
    let netlist = k.pad_netlist().await?;
    let mut codes = NetCodes::from_board(&k.board_nets().await.unwrap_or_default());
    let mut assigned: HashMap<(String, String), String> = HashMap::new();
    let mut pad_nets: HashMap<String, PadNetAssign> = HashMap::new();
    let mut results = Vec::new();

    for (a, b, hint) in pairs {
        let pas = find_entries(&netlist, &a.reference, &a.pin)?;
        let pbs = find_entries(&netlist, &b.reference, &b.pin)?;
        let current_a = assigned
            .get(&(a.reference.clone(), a.pin.clone()))
            .cloned()
            .or_else(|| first_named_net(&pas));
        let current_b = assigned
            .get(&(b.reference.clone(), b.pin.clone()))
            .cloned()
            .or_else(|| first_named_net(&pbs));
        let fallback = format!("Net_{}_{}", a.reference, a.pin);
        let net = resolve_net_name(
            current_a.as_deref(),
            current_b.as_deref(),
            hint.as_deref(),
            &fallback,
        )
        .map_err(|e| {
            format!(
                "couldn't connect {}.{} to {}.{}: {e}",
                a.reference, a.pin, b.reference, b.pin
            )
        })?;
        let code = codes.code_for(&net);
        for pa in &pas {
            pad_nets.insert(pad_id_of(pa)?, PadNetAssign::Named(net.clone(), code));
        }
        for pb in &pbs {
            pad_nets.insert(pad_id_of(pb)?, PadNetAssign::Named(net.clone(), code));
        }
        assigned.insert((a.reference.clone(), a.pin.clone()), net.clone());
        assigned.insert((b.reference.clone(), b.pin.clone()), net.clone());
        results.push(serde_json::json!({
            "ref1": a.reference,
            "pin1": a.pin,
            "ref2": b.reference,
            "pin2": b.pin,
            "net": net,
            "pads": pas.len() + pbs.len(),
        }));
    }

    apply_pad_nets(k, &pad_nets).await?;
    Ok(results)
}

/// Take pins off their nets (`Pad.net` → code 0 / `"unconnected"`). Every
/// pad that shares the pin number is cleared (thermal clusters). Idempotent
/// if already unconnected. Does not rip copper.
pub async fn disconnect_pins(k: &Kicad, pins: &[PinRef]) -> Result<Vec<serde_json::Value>, String> {
    if pins.is_empty() {
        return Err("disconnect_pin needs at least one pin".into());
    }
    if pins.len() > crate::place::PLACE_MAX {
        return Err(format!(
            "disconnect_many max {} pins (got {})",
            crate::place::PLACE_MAX,
            pins.len()
        ));
    }
    let netlist = k.pad_netlist().await?;
    let mut pad_nets: HashMap<String, PadNetAssign> = HashMap::new();
    let mut results = Vec::new();
    for pin in pins {
        let entries = find_entries(&netlist, &pin.reference, &pin.pin)?;
        let was = first_named_net(&entries);
        for entry in &entries {
            pad_nets.insert(pad_id_of(entry)?, PadNetAssign::Unconnected);
        }
        results.push(serde_json::json!({
            "reference": pin.reference,
            "pin": pin.pin,
            "pads": entries.len(),
            "was": was,
        }));
    }
    apply_pad_nets(k, &pad_nets).await?;
    Ok(results)
}

#[derive(Clone, Debug)]
enum PadNetAssign {
    Named(String, i32),
    Unconnected,
}

impl PadNetAssign {
    fn payload(&self) -> Vec<u8> {
        match self {
            Self::Named(name, code) => encode_net(name, *code),
            Self::Unconnected => encode_unconnected(),
        }
    }
}

async fn apply_pad_nets(k: &Kicad, pad_nets: &HashMap<String, PadNetAssign>) -> Result<(), String> {
    let fps = k
        .raw_items(vec![PcbObjectTypeCode::new_footprint().code])
        .await?;
    let mut updates = Vec::new();
    let mut found: HashMap<String, ()> = HashMap::new();
    for fp in fps {
        if let Some(patched) = patch_footprint_pads(&fp, pad_nets, &mut found)? {
            updates.push(patched);
        }
    }
    let missing: Vec<_> = pad_nets
        .keys()
        .filter(|id| !found.contains_key(*id))
        .cloned()
        .collect();
    if !missing.is_empty() {
        return Err(format!(
            "pad {} is not nested in any footprint — cannot UpdateItems a free pad (KiCad: pad must live in a footprint)",
            missing.join(", ")
        ));
    }
    k.update_items(updates).await?;
    Ok(())
}
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
